emrebuyukonder/Boss-DS-1-Clone/media/IMG_3559 2.JPG

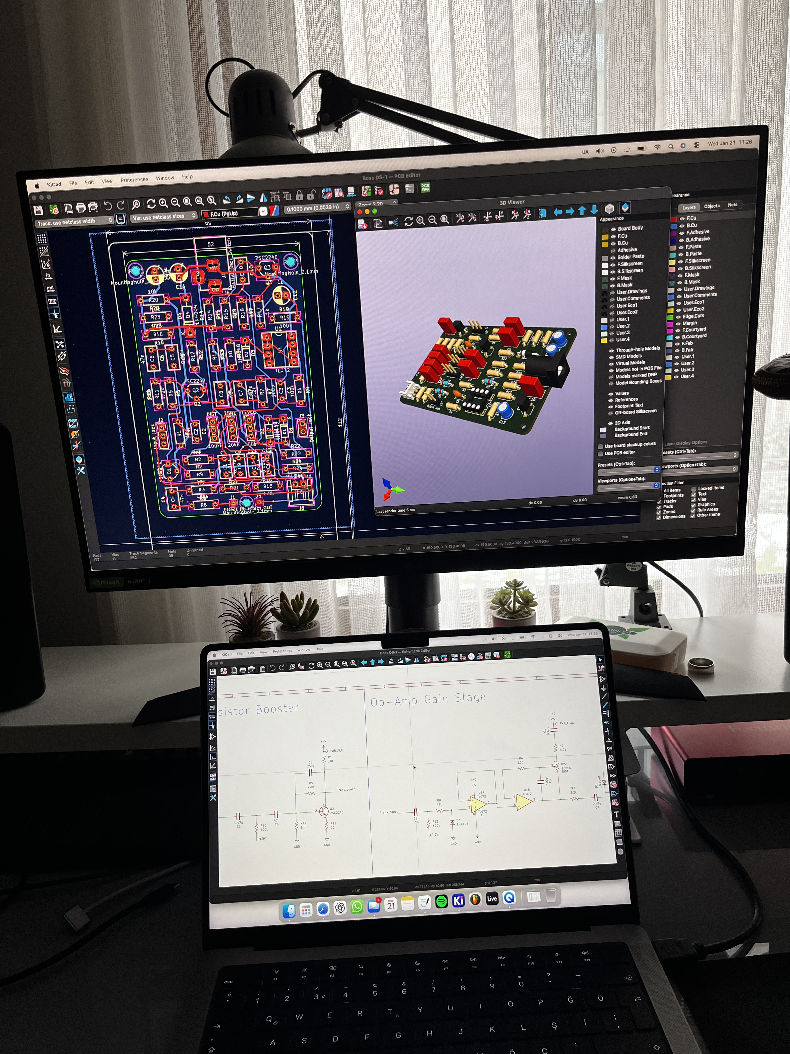
media/IMG_3559 2.JPG
